Pabloale96/Tp-Prof/Modelos/Piezas de un extraño 3D/shaft_coupler_hex.stl

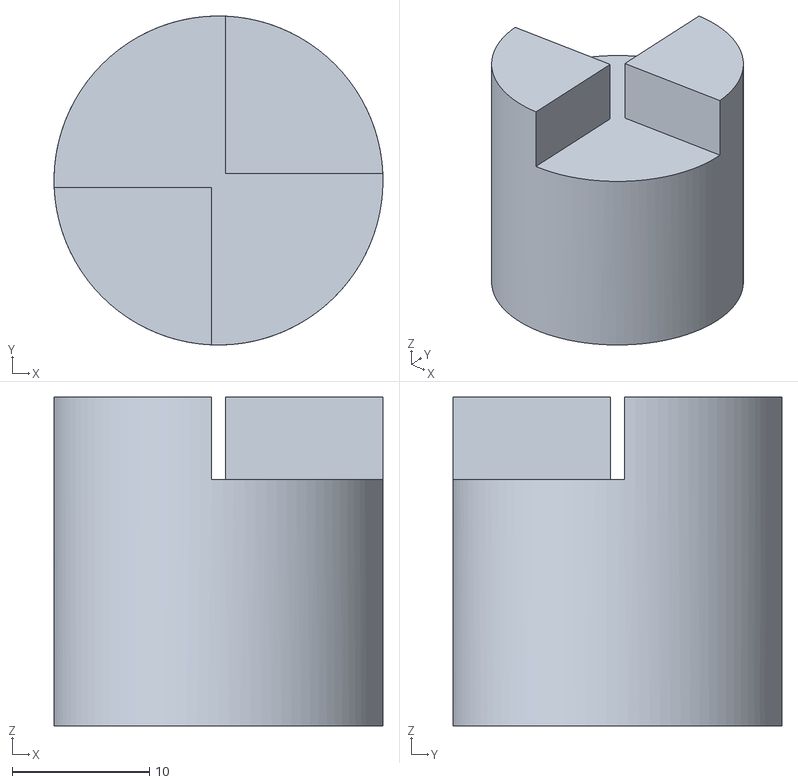
[picture p42: CAD file, 2021-04-10, last stored version]
Modelos/Piezas de un extraño 3D/shaft_coupler_hex.stl
24.0 x 24.0 x 24.0
